Dresnaught/swr-stm32f4-cmake/Core/Inc/menu_calibration.h

#ifndef MENU_CALIBRATION_H
#define MENU_CALIBRATION_H

#include "calibration.h"

// Handle interactive multi-point calibration workflow for FWD, REF, or RAD
void calibrationMenu(CalChannelType ch);

#endif // MENU_CALIBRATION_H
